Pako2/RadioESP32/assets/EditIRcommand.png

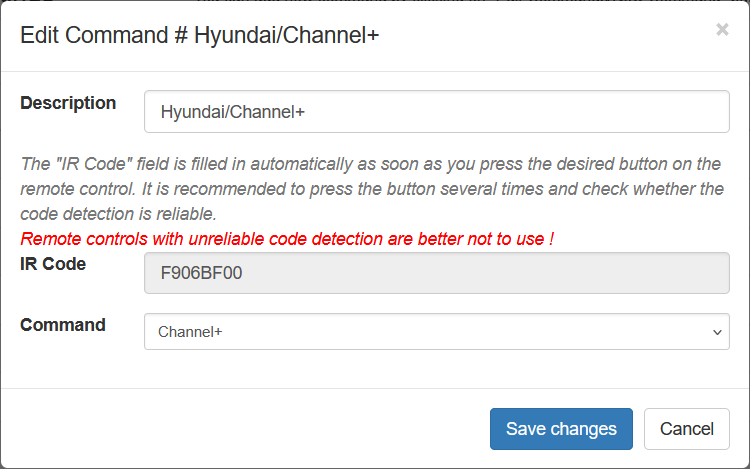
assets/EditIRcommand.png
